Mihai-29/Autonomous-thermal-camera/images/Picture2.png

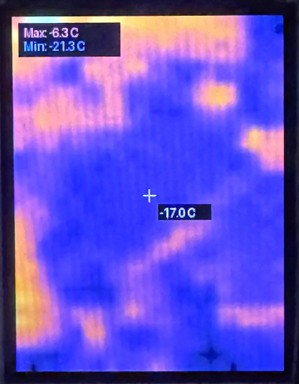
images/Picture2.png
